JackMillen/Macropad-V2-Mini/PCB/KiCad/Macropad v2.kicad_sch

## KiCad design PCB/KiCad/Macropad v2.kicad_sch (2022-05-16)

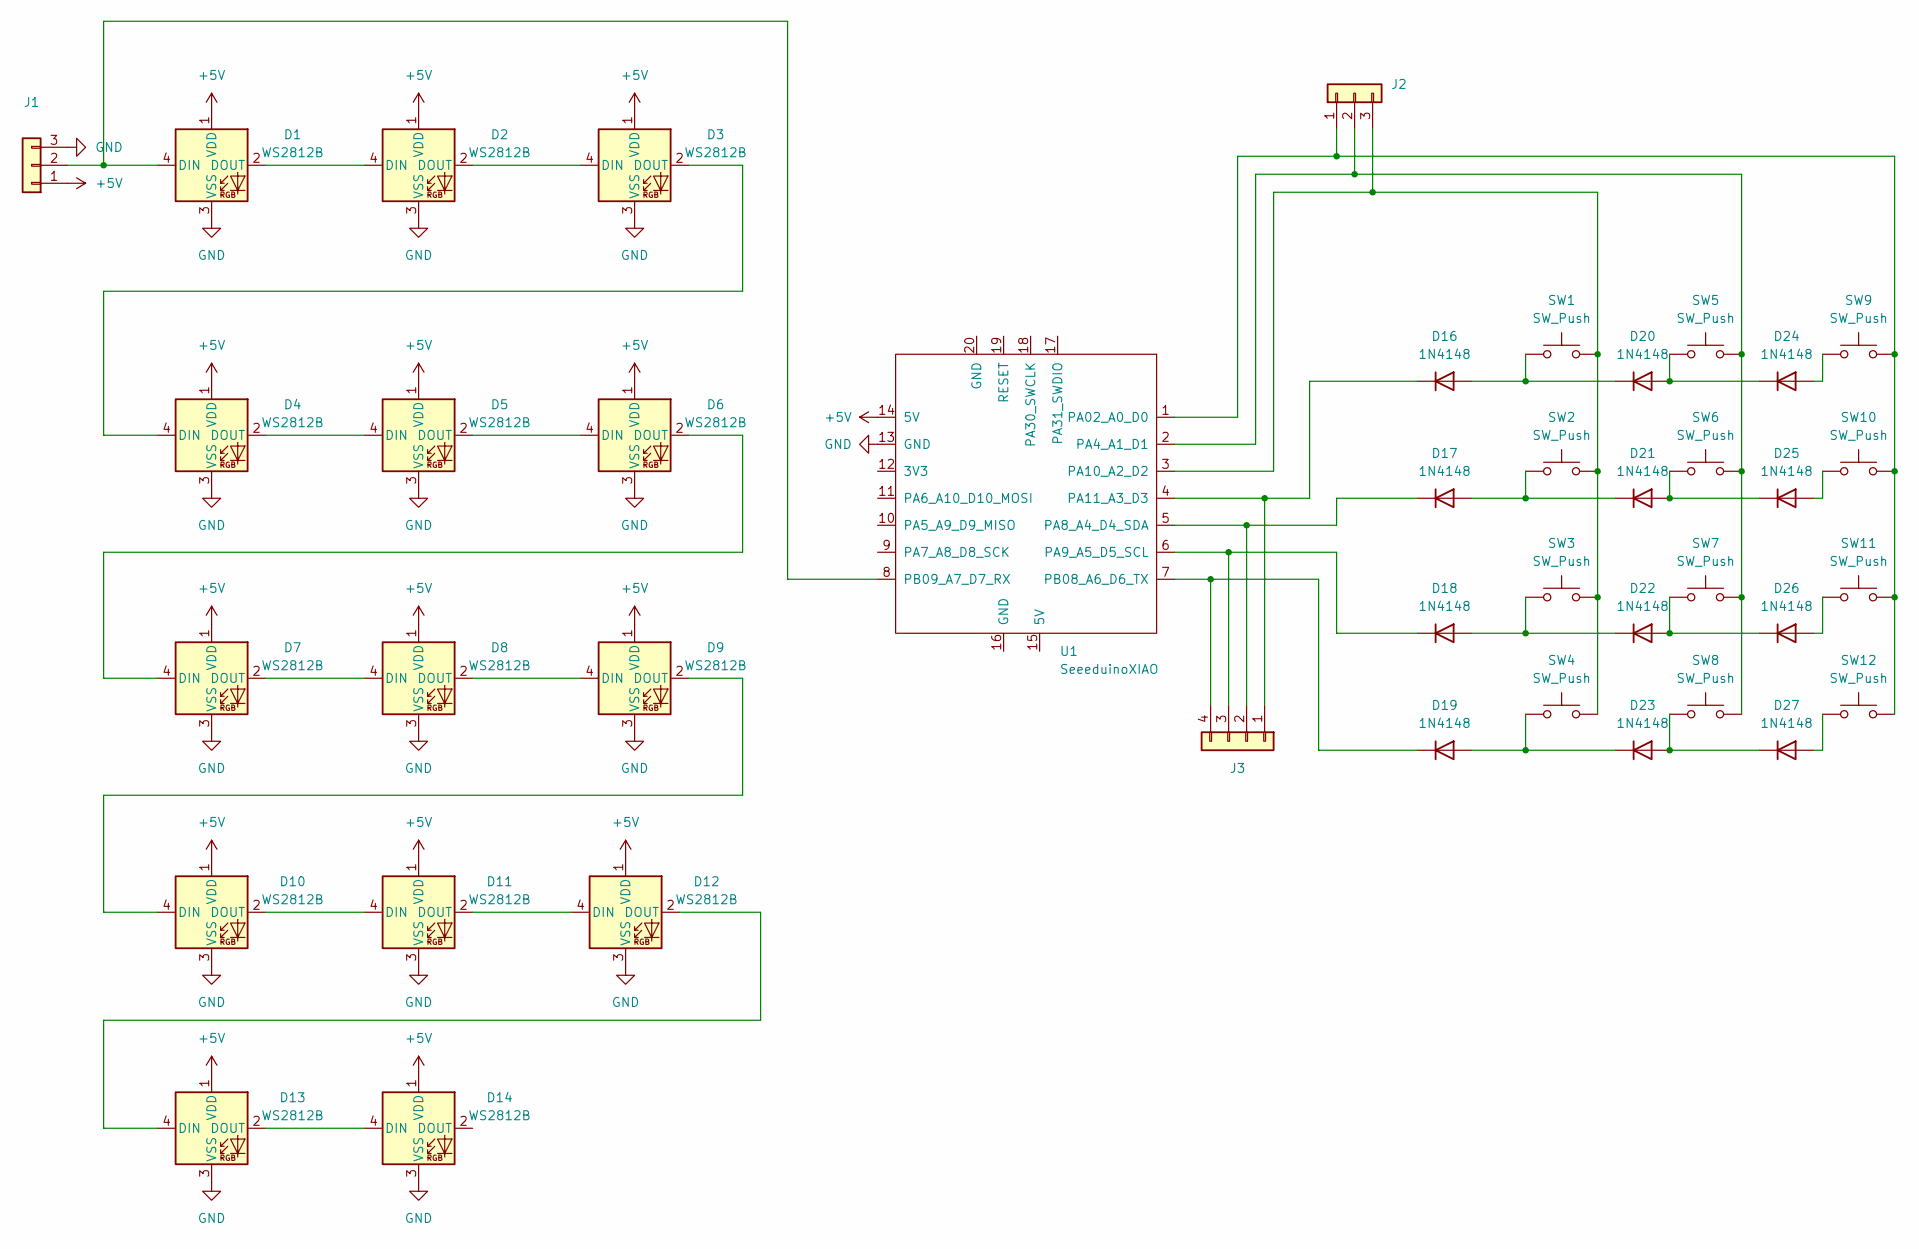
[picture p9: schematic Macropad v2.kicad_sch]

Parts:
D1, D2, D3, D4, D5, D6, D7, D8, D9, D10, D11, D12, D13, D14: WS2812B; LED_WS2812B_PLCC4_5.0x5.0mm_P3.2mm
D16, D17, D18, D19, D20, D21, D22, D23, D24, D25, D26, D27: 1N4148; D_DO-35_SOD27_P7.62mm_Horizontal
J1, J2, J3: (no value)
SW1, SW2, SW3, SW4, SW5, SW6, SW7, SW8, SW9, SW10, SW11, SW12: SW_Push; SW_Cherry_MX_PCB
U1: SeeeduinoXIAO; Seeeduino XIAO-MOUDLE14P-2.54-21X17.8MM

Connections:
+5V: D1.1 (VDD), D2.1 (VDD), D3.1 (VDD), D4.1 (VDD), D5.1 (VDD), D6.1 (VDD), D7.1 (VDD), D8.1 (VDD), D9.1 (VDD), D10.1 (VDD), D11.1 (VDD), D12.1 (VDD), D13.1 (VDD), D14.1 (VDD), J1.1, U1.14 (5V)
GND: D1.3 (VSS), D2.3 (VSS), D3.3 (VSS), D4.3 (VSS), D5.3 (VSS), D6.3 (VSS), D7.3 (VSS), D8.3 (VSS), D9.3 (VSS), D10.3 (VSS), D11.3 (VSS), D12.3 (VSS), D13.3 (VSS), D14.3 (VSS), J1.3, U1.13 (GND)
unnamed: D1.2 (DOUT), D2.4 (DIN)
unnamed: D1.4 (DIN), J1.2, U1.8 (PB09_A7_D7_RX)
unnamed: D2.2 (DOUT), D3.4 (DIN)
unnamed: D3.2 (DOUT), D4.4 (DIN)
unnamed: D4.2 (DOUT), D5.4 (DIN)
unnamed: D5.2 (DOUT), D6.4 (DIN)
unnamed: D6.2 (DOUT), D7.4 (DIN)
unnamed: D7.2 (DOUT), D8.4 (DIN)
unnamed: D8.2 (DOUT), D9.4 (DIN)
unnamed: D10.2 (DOUT), D11.4 (DIN)
unnamed: D9.2 (DOUT), D10.4 (DIN)
unnamed: D11.2 (DOUT), D12.4 (DIN)
unnamed: D12.2 (DOUT), D13.4 (DIN)
unnamed: D13.2 (DOUT), D14.4 (DIN)
unnamed: D16.1 (K), J3.1, U1.4 (PA11_A3_D3)
unnamed: D16.2 (A), D20.1 (K), SW1.1
unnamed: D17.1 (K), J3.2, U1.5 (PA8_A4_D4_SDA)
unnamed: D17.2 (A), D21.1 (K), SW2.1
unnamed: D18.1 (K), J3.3, U1.6 (PA9_A5_D5_SCL)
unnamed: D18.2 (A), D22.1 (K), SW3.1
unnamed: D19.1 (K), J3.4, U1.7 (PB08_A6_D6_TX)
unnamed: D19.2 (A), D23.1 (K), SW4.1
unnamed: D20.2 (A), D24.1 (K), SW5.1
unnamed: D21.2 (A), D25.1 (K), SW6.1
unnamed: D22.2 (A), D26.1 (K), SW7.1
unnamed: D23.2 (A), D27.1 (K), SW8.1
unnamed: D24.2 (A), SW9.1
unnamed: D25.2 (A), SW10.1
unnamed: D26.2 (A), SW11.1
unnamed: D27.2 (A), SW12.1
unnamed: J2.1, SW9.2, SW10.2, SW11.2, SW12.2, U1.1 (PA02_A0_D0)
unnamed: J2.2, SW5.2, SW6.2, SW7.2, SW8.2, U1.2 (PA4_A1_D1)
unnamed: J2.3, SW1.2, SW2.2, SW3.2, SW4.2, U1.3 (PA10_A2_D2)
